SPARC-Auburn/THAD/CV_Control/grayhand.jpg

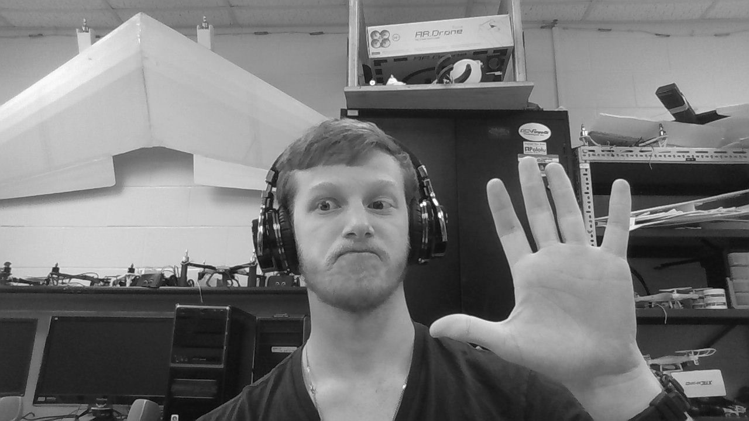
CV_Control/grayhand.jpg
