SPARC-Auburn/THAD/CV_Control/IMG_6559.JPG

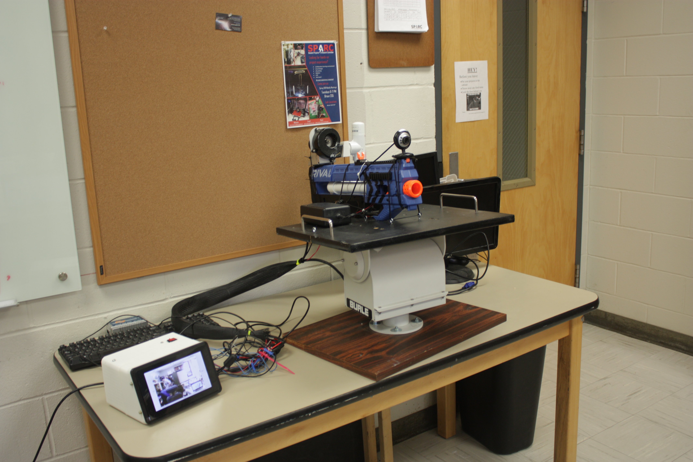
CV_Control/IMG_6559.JPG
