SPARC-Auburn/THAD/CV_Control/IMG_6560.JPG

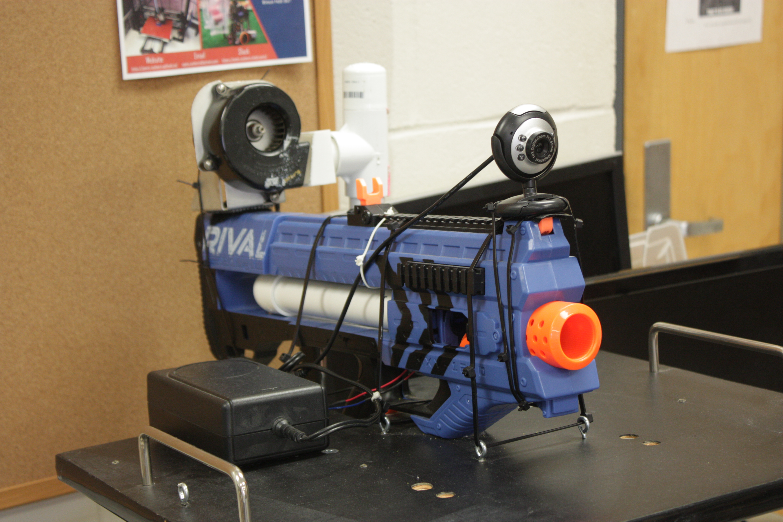
CV_Control/IMG_6560.JPG
