SPARC-Auburn/THAD/CV_Control/IMG_6562.JPG

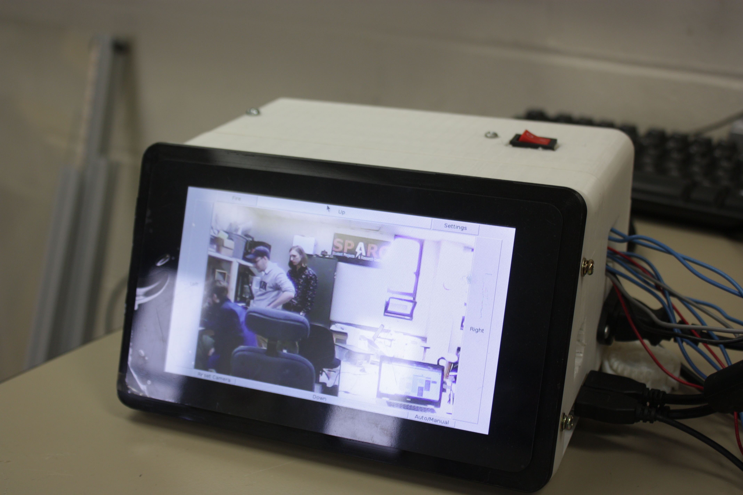
CV_Control/IMG_6562.JPG
