SPARC-Auburn/THAD/CV_Control/IMG_6564.JPG

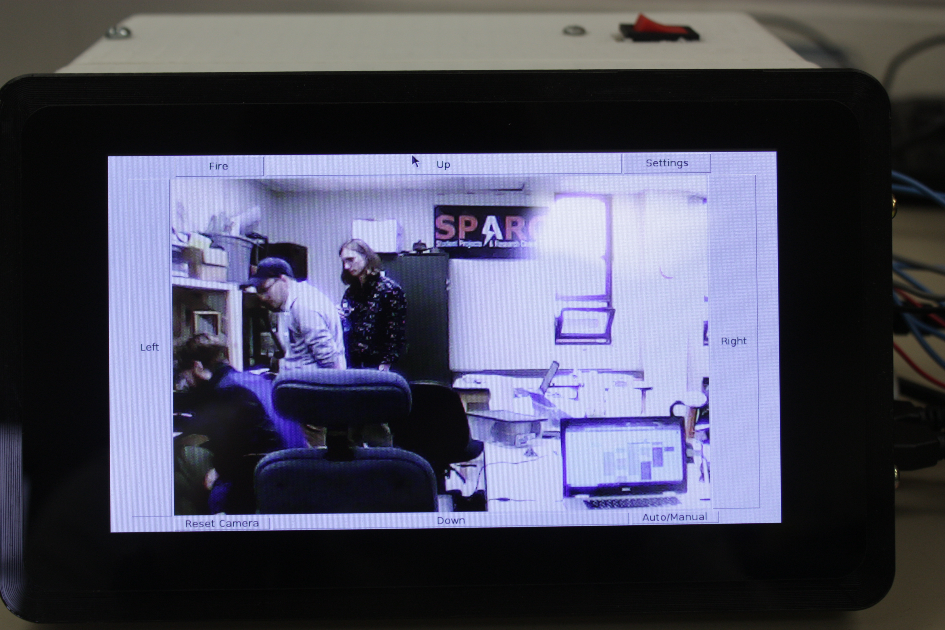
CV_Control/IMG_6564.JPG
