SPARC-Auburn/THAD/CV_Control/PCServer.py

import numpy as np
import cv2
import serial
import sys
import time
import math
import socket
#from mainWindow import mainWindow
#!/usr/bin/env python
 
import socket


TCP_IP = '127.0.0.1'
TCP_PORT = 5005
BUFFER_SIZE = 1024  # Normally 1024, but we want fast response

s = socket.socket(socket.AF_INET, socket.SOCK_STREAM)
s.bind((TCP_IP, TCP_PORT))
s.listen(1)
while 1:
    conn, addr = s.accept()
    print 'Connection address:', addr
    while 1:
        data = conn.recv(BUFFER_SIZE)
        if data == "close": break
        print "received data:", data
        conn.send("Hello, THAD!") 
