SPARC-Auburn/THAD/CV_Control/face_recog.py

import io
import picamera
import cv2
import numpy
import time

#Create a memory stream so photos doesn't need to be saved in a file
stream = io.BytesIO()

#Get the picture (low resolution, so it should be quite fast)
#Here you can also specify other parameters (e.g.:rotate the image)
with picamera.PiCamera() as camera:
    #camera.start_preview()
    camera.resolution = (960, 540)
    camera.vflip = False
    camera.capture(stream, format='jpeg')
    #camera.stop_preview()    

#Convert the picture into a numpy array
buff = numpy.fromstring(stream.getvalue(), dtype=numpy.uint8)

#Now creates an OpenCV image
image = cv2.imdecode(buff, 1)

#Load a cascade file for detecting faces
face_cascade = cv2.CascadeClassifier('/usr/share/opencv/haarcascades/haarcascade_frontalface_alt.xml')

#Convert to grayscale
gray = cv2.cvtColor(image,cv2.COLOR_BGR2GRAY)

#Look for faces in the image using the loaded cascade file
faces = face_cascade.detectMultiScale(gray, 1.1, 5)

print "Found "+str(len(faces))+" face(s)"

#Draw a rectangle around every found face
for (x,y,w,h) in faces:
    cv2.rectangle(image,(x,y),(x+w,y+h),(255,255,0),2)
cv2.imshow('result',image)
cv2.waitKey(0)
cv2.destroyAllWindows()
#Save the result image
#cv2.imwrite('result.jpg',image)
